ts-manuel/Battery-Powered-PSU/software/PowerSupply.X/src/graphics/GLCD_Fonts.c

/*
 * GLCD_Fonts.c
 *
 *  Created on: 30 gen 2018
 *      Author: Manuel
 */

#include <stdint.h>
#include "GLCD_Fonts.h"

const Font6_t font_4x5 = {
    ' ', 58, 8, 6, 5,   //offset, numCharacters, stride, maxX, maxY
    {
    {2, 5, {0x00, 0x00, 0x00, 0x00, 0x00, 0x00}},   // SPACE
    {4, 5, {0xFF, 0xFF, 0xFF, 0xFF, 0xFF, 0xFF}},   // !
    {4, 5, {0xFF, 0xFF, 0xFF, 0xFF, 0xFF, 0xFF}},   // "
    {4, 5, {0xFF, 0xFF, 0xFF, 0xFF, 0xFF, 0xFF}},   // #
    {4, 5, {0xFF, 0xFF, 0xFF, 0xFF, 0xFF, 0xFF}},   // $
    {6, 5, {0x13, 0x09, 0x04, 0x12, 0x19, 0x00}},   // %
    {4, 5, {0xFF, 0xFF, 0xFF, 0xFF, 0xFF, 0xFF}},   // &
    {4, 5, {0xFF, 0xFF, 0xFF, 0xFF, 0xFF, 0xFF}},   // '
    {4, 5, {0xFF, 0xFF, 0xFF, 0xFF, 0xFF, 0xFF}},   // (
    {4, 5, {0xFF, 0xFF, 0xFF, 0xFF, 0xFF, 0xFF}},   // )
    {4, 5, {0xFF, 0xFF, 0xFF, 0xFF, 0xFF, 0xFF}},   // *
    {4, 5, {0xFF, 0xFF, 0xFF, 0xFF, 0xFF, 0xFF}},   // +
    {4, 5, {0xFF, 0xFF, 0xFF, 0xFF, 0xFF, 0xFF}},   // ,
    {4, 5, {0x04, 0x04, 0x04, 0x00, 0x00, 0x00}},   // -
    {2, 5, {0x10, 0x00, 0x00, 0x00, 0x00, 0x00}},   // . 
    {6, 5, {0x10, 0x08, 0x04, 0x02, 0x01, 0x00}},   // /
    {5, 5, {0x1F, 0x11, 0x11, 0x1F, 0x00, 0x00}},   // 0
    {4, 5, {0x11, 0x1F, 0x10, 0x00, 0x00, 0x00}},   // 1
    {5, 5, {0x1D, 0x15, 0x15, 0x17, 0x00, 0x00}},   // 2
    {5, 5, {0x15, 0x15, 0x15, 0x1F, 0x00, 0x00}},   // 3
    {5, 5, {0x07, 0x04, 0x04, 0x1F, 0x00, 0x00}},   // 4
    {5, 5, {0x17, 0x15, 0x15, 0x1D, 0x00, 0x00}},   // 5
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
    {7, 9, {0xEE, 0x00, 0x11, 0x01,  0x11, 0x01, 0x11, 0x01,  0x11, 0x01, 0xEE, 0x00,  0x00, 0x00}},   // 8
    {7, 9, {0x0E, 0x00, 0x11, 0x01,  0x11, 0x01, 0x11, 0x01,  0x11, 0x01, 0xEE, 0x00,  0x00, 0x00}},   // 9
    {7, 9, {0x00, 0x00, 0x00, 0x00,  0x83, 0x01, 0x83, 0x01,  0x00, 0x00, 0x00, 0x00,  0x00, 0x00}}    // :
    }
};
