ts-manuel/Battery-Powered-PSU/software/PowerSupply.X/src/menu/icons.c

/* 
 * File:    icons.c
 * Author:  Manuel
 * Date:    27/10/2018
 * 
 * Comments:
 */

#include "icons.h"

static const uint8_t mainPageData[] = {
    0x01, 0x45, 0x7D, 0x05, 0x01, 0x71, 0x11, 0x11, 0x7D, 0x01, 0x05, 0x09, 0x11, 0x21, 0x41, 0x01, 
    0x45, 0x7D, 0x05, 0x01, 0x7D, 0x45, 0x45, 0x7D, 0x01, 0x05, 0x09, 0x11, 0x21, 0x41, 0x01, 0x45, 
    0x7D, 0x05, 0x01, 0x7D, 0x55, 0x55, 0x7D, 0x01, 0x01, 0x01, 0x01, 0x01, 0x01, 0x45, 0x7D, 0x05, 
    0x01, 0x7D, 0x55, 0x55, 0x5D, 0x01, 0x01, 0x29, 0x01, 0x01, 0x71, 0x11, 0x11, 0x7D, 0x01, 0x75, 
    0x55, 0x55, 0x5D, 0x01, 0x01, 0x01, 0x01, 0x01, 0x01, 0x01, 0x01, 0x01, 0x01, 0x01, 0x01, 0x01, 
    0x01, 0x01, 0x01, 0x01, 0x01, 0x01, 0x01, 0x01, 0x01, 0x01, 0x01, 0x01, 0x01, 0x01, 0x01, 0x01, 
    0x01, 0x01, 0x01, 0x01, 0x01, 0x01, 0x01, 0x01, 0x01, 0x01, 0x01, 0x01, 0x01, 0x01, 0x01, 0x01, 
    0x01, 0x01, 0x01, 0x01, 0x01, 0x01, 0x39, 0x45, 0x4D, 0x5D, 0x7D, 0x7D, 0x7D, 0x7D, 0x7D, 0x01, 
    0x01, 0x7D, 0x45, 0x45, 0x01, 0x7D, 0x11, 0x11, 0x7D, 0x01, 0x45, 0x7D, 0x05, 0x01, 0xFF, 0x00, 
    0x00, 0x00, 0x00, 0x00, 0x00, 0x00, 0x00, 0x00, 0x00, 0x00, 0x00, 0x00, 0x00, 0x00, 0x00, 0x00, 
    0x00, 0x00, 0x00, 0x00, 0x00, 0x00, 0x00, 0x00, 0x00, 0x00, 0x00, 0x00, 0x00, 0x00, 0x00, 0x00, 
    0x00, 0x00, 0x00, 0x00, 0x00, 0x00, 0x00, 0x00, 0x00, 0x00, 0x00, 0x00, 0x00, 0x00, 0x00, 0xFF, 
    0xFF, 0x01, 0x7D, 0x45, 0x45, 0x01, 0x7D, 0x11, 0x11, 0x7D, 0x01, 0x5D, 0x55, 0x75, 0x01, 0xFF, 
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
};
const GLCD_Bitmap_t errorsICO = { 32, 32, errorsBMP };

static const uint8_t errorSmallBMP[] = {
	0x00, 0x00, 0x00, 0xF6, 0xF6, 0x00, 0x00, 0x00, 0x00, 
};
const GLCD_Bitmap_t errorSmallICO = { 9, 7, errorSmallBMP };
