ts-manuel/Battery-Powered-PSU/software/PowerSupply.X/src/menu/menu_main.h

/* 
 * File:    menu_main.h
 * Author:  Manuel
 * Date:    10/10/2018
 * 
 * Comments: Main page of the menu
 */

#ifndef SRC_MENU_MENU_MAIN_H
#define	SRC_MENU_MENU_MAIN_H

#include "mcc.h"
#include "menu.h"




#endif	/* SRC_MENU_MENU_MAIN_H */
