ts-manuel/Battery-Powered-PSU/software/PowerSupply.X/src/globalVariables.c

#include "globalVariables.h"

PSU_ChannelGlobalVariables_t PSU_GlobalVariables[2];

uint8_t LCD_Backlight       = 128;  //Intensity of the screen backlight
uint8_t LCD_TimeoutSeconds  = 60;   //Timeout for the screen backlight tornoff
