ts-manuel/Battery-Powered-PSU/software/PowerSupply.X/src/menu/icons.h

/* 
 * File:    icons.h
 * Author:  Manuel
 * Date:    27/10/2018
 * 
 * Comments:
 */


#ifndef _SRC_MENU_ICINS_H
#define	_SRC_MENU_ICINS_H

#include "graphics/GLCD.h"

extern const GLCD_Bitmap_t mainPageBMP;
extern const GLCD_Bitmap_t returnICO;
extern const GLCD_Bitmap_t settingsICO;
extern const GLCD_Bitmap_t batteryICO;
extern const GLCD_Bitmap_t calibrationICO;
extern const GLCD_Bitmap_t errorsICO;
extern const GLCD_Bitmap_t errorSmallICO;

#endif	/* _SRC_MENU_ICINS_H */
